OLIMEX/Neo6502/HARDWARE/Neo6502-rev-B1/3d/USB-A-SMT-6.3H_HOST_Female(87583-2010RLF).STEP

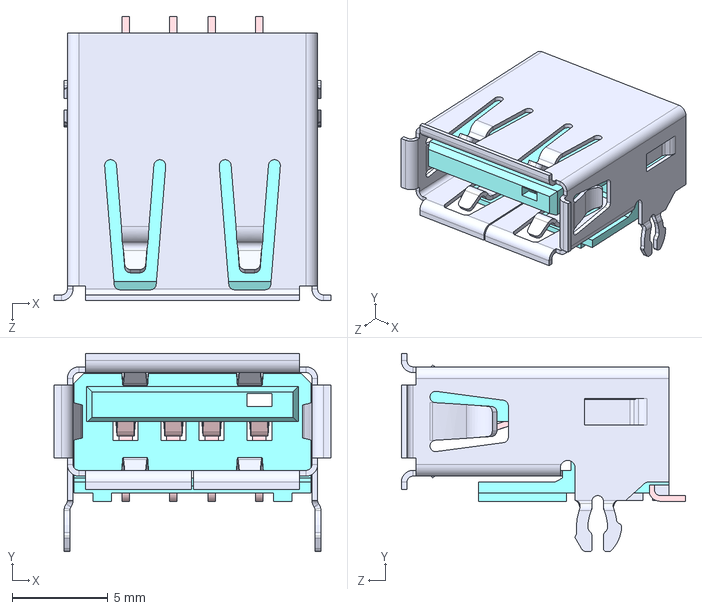
[picture p46: CAD file, 2023-08-04]
HARDWARE/Neo6502-rev-B1/3d/USB-A-SMT-6.3H_HOST_Female(87583-2010RLF).STEP
14.5 x 10.4 x 14.9 mm
