OLIMEX/Neo6502/HARDWARE/Neo6502-rev-B1/3d/USB-A-SMT-6.3H_HOST_Female(USB1046-GF-0190-L-B-A).STEP

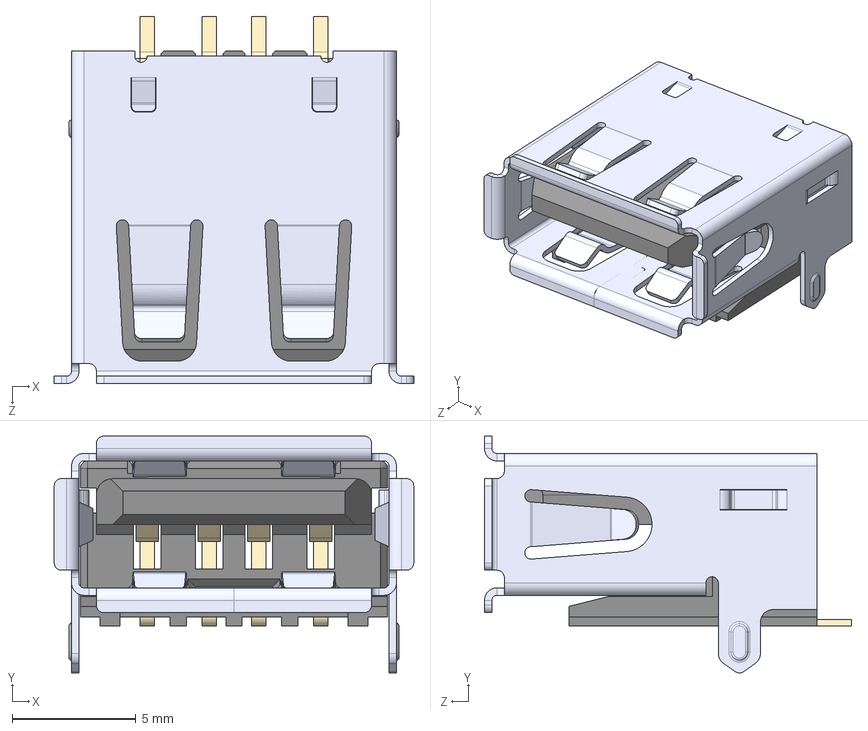
[picture p47: CAD file, 2023-08-04]
HARDWARE/Neo6502-rev-B1/3d/USB-A-SMT-6.3H_HOST_Female(USB1046-GF-0190-L-B-A).STEP
14.5 x 9.55 x 14.8 mm
