OLIMEX/Neo6502/HARDWARE/Neo6502-rev-B1/3d/SOT-23-5.step

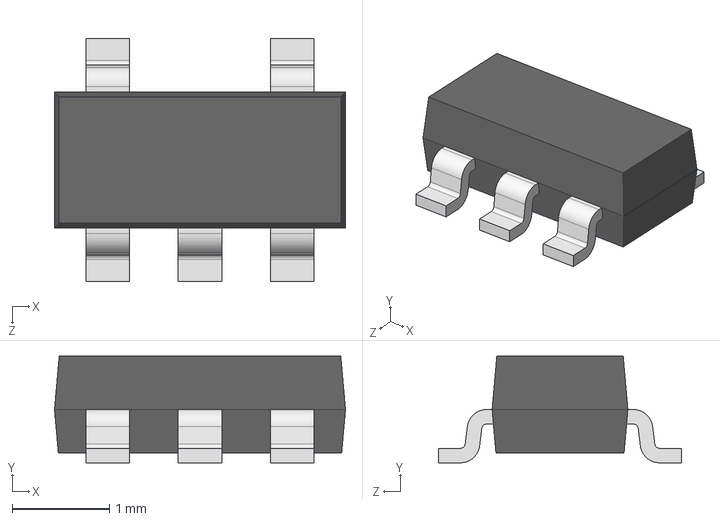
[picture p48: CAD file, 2023-08-04]
HARDWARE/Neo6502-rev-B1/3d/SOT-23-5.step
3.00 x 1.10 x 2.50 mm
