OLIMEX/Neo6502/HARDWARE/Neo6502-rev-B1/3d/HDMI_19POS_SMD_Wurth_Electronic-685119134923.stp

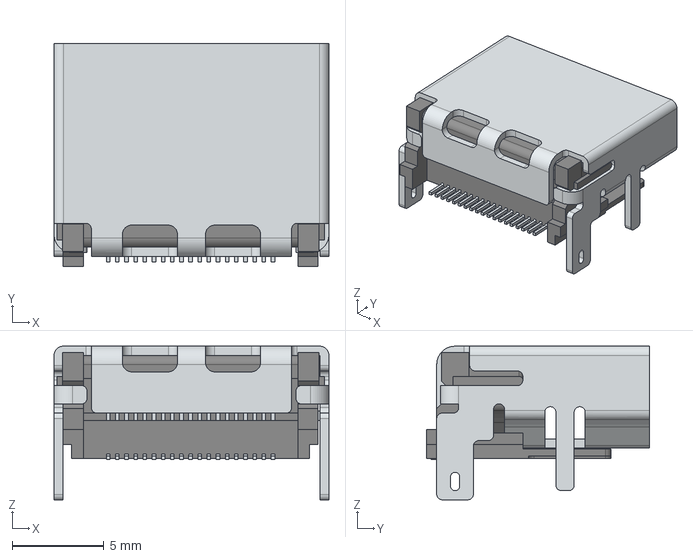
[picture p49: CAD file, 2023-08-04]
HARDWARE/Neo6502-rev-B1/3d/HDMI_19POS_SMD_Wurth_Electronic-685119134923.stp
15.0 x 12.2 x 8.38 mm
