OLIMEX/Neo6502/HARDWARE/Neo6502-rev-B1/3d/L-CD32_shielded.step

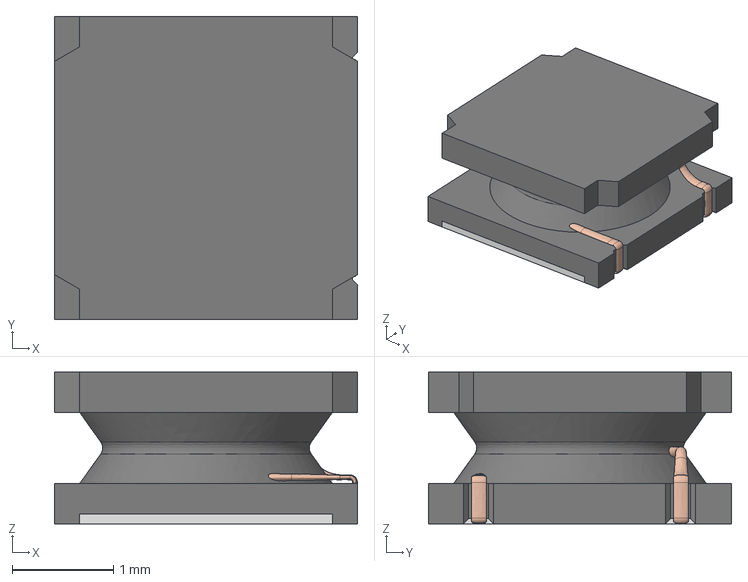
[picture p50: CAD file, 2023-08-04]
HARDWARE/Neo6502-rev-B1/3d/L-CD32_shielded.step
3.00 x 3.00 x 1.50 mm
