OLIMEX/Neo6502/HARDWARE/Neo6502-rev-B1/3d/SOT-23.step

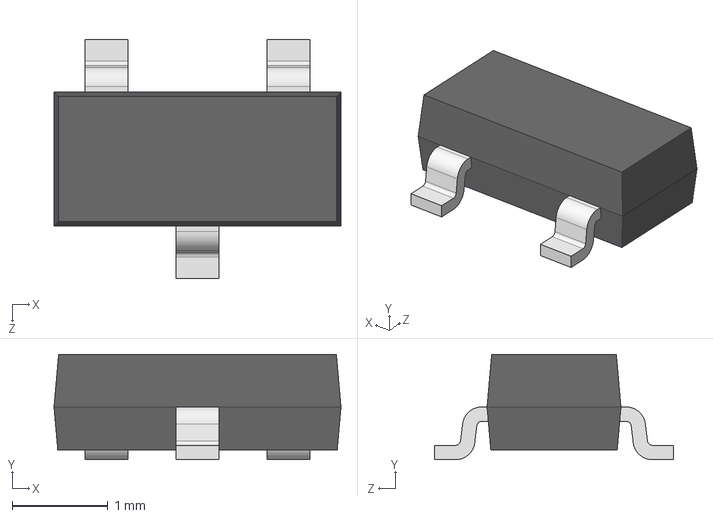
[picture p51: CAD file, 2023-08-04]
HARDWARE/Neo6502-rev-B1/3d/SOT-23.step
3.00 x 1.10 x 2.50 mm
