OLIMEX/Neo6502/SOFTWARE/Memory Emulator/NEO6502 v0.01/msbasic.cpp

// 
// Author: Rien Matthijsse
// 

#include "msbasic.h"

uint8_t msbasic_bin[] = {
	0x3f, 0xa6, 0x60, 0xa5, 0x43, 0xaa, 0x0c, 0xa7, 0x26, 0xa9, 0x04, 0xad, 0x52, 0xa9, 0xb9, 0xa7, 0xb9, 0xa6, 0x91, 0xa6, 0x3c, 0xa7, 0x23, 0xa6,
	0x9c, 0xa6, 0xe6, 0xa6, 0x4f, 0xa7, 0x3d, 0xa6, 0x5f, 0xa7, 0x80, 0xa6, 0x37, 0xb4, 0x68, 0xfd, 0xf6, 0xff, 0xe1, 0xaf, 0x2e, 0xb4, 0x2f, 0xa8,
	0x66, 0xa6, 0xbd, 0xa4, 0x80, 0xa4, 0x65, 0xa4, 0xe1, 0xb7, 0x6b, 0xb8, 0xfe, 0xb7, 0x0a, 0x00, 0xb1, 0xaf, 0xd2, 0xaf, 0xb5, 0xba, 0xc9, 0xbb,
	0xc3, 0xb5, 0x24, 0xbb, 0x05, 0xbc, 0x0c, 0xbc, 0x55, 0xbc, 0xa2, 0xbc, 0x24, 0xb4, 0x92, 0xb3, 0x90, 0xb0, 0xc3, 0xb3, 0xa1, 0xb3, 0x02, 0xb3,
	0x16, 0xb3, 0x42, 0xb3, 0x4d, 0xb3, 0x79, 0x74, 0xb4, 0x79, 0x5d, 0xb4, 0x7b, 0x03, 0xb6, 0x7b, 0xd5, 0xb6, 0x7f, 0xbe, 0xba, 0x50, 0x6c, 0xac,
	0x46, 0x69, 0xac, 0x7d, 0xf7, 0xba, 0x5a, 0xdb, 0xab, 0x64, 0x99, 0xac, 0x45, 0x4e, 0xc4, 0x46, 0x4f, 0xd2, 0x4e, 0x45, 0x58, 0xd4, 0x44, 0x41,
	0x54, 0xc1, 0x49, 0x4e, 0x50, 0x55, 0xd4, 0x44, 0x49, 0xcd, 0x52, 0x45, 0x41, 0xc4, 0x4c, 0x45, 0xd4, 0x47, 0x4f, 0x54, 0xcf, 0x52, 0x55, 0xce,
	0x49, 0xc6, 0x52, 0x45, 0x53, 0x54, 0x4f, 0x52, 0xc5, 0x47, 0x4f, 0x53, 0x55, 0xc2, 0x52, 0x45, 0x54, 0x55, 0x52, 0xce, 0x52, 0x45, 0xcd, 0x53,
	0x54, 0x4f, 0xd0, 0x4f, 0xce, 0x4e, 0x55, 0x4c, 0xcc, 0x57, 0x41, 0x49, 0xd4, 0x4c, 0x4f, 0x41, 0xc4, 0x53, 0x41, 0x56, 0xc5, 0x44, 0x45, 0xc6,
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
	0xea, 0xea, 0xea, 0xea, 0xea, 0xea, 0xea, 0xea, 0x29, 0x7f, 0xc9, 0x0f, 0xd0, 0x08, 0x48, 0xa5, 0x64, 0x49, 0xff, 0x85, 0x64, 0x68, 0x60, 0xa6,
	0xc3, 0xa0, 0x04, 0x84, 0x60, 0xbd, 0x00, 0x00, 0xc9, 0x20, 0xf0, 0x3b, 0x85, 0x5c, 0xc9, 0x22, 0xf0, 0x5a, 0x24, 0x60, 0x70, 0x31, 0xc9, 0x3f,
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
};
