OLIMEX/Neo6502/SOFTWARE/Memory Emulator/NEO6502 v0.01/ewoz.cpp

// 
// Author: Rien Matthijsse
// 

#include "ewoz.h"

uint8_t ewoz_bin[] = {
	0x20, 0xfc, 0x60, 0xfd, 0x46, 0xfd, 0x00, 0x00, 0x00, 0x00, 0x00, 0x00, 0x00, 0x00, 0x00, 0x00, 0x00, 0x00, 0x00, 0x00, 0x00, 0x00, 0x00, 0x00,
	0x00, 0x00, 0x00, 0x00, 0x00, 0x00, 0x00, 0x00, 0xd8, 0x58, 0xa2, 0xff, 0x9a, 0xa0, 0x7f, 0x8c, 0x12, 0xd0, 0xa9, 0xa7, 0x8d, 0x11, 0xd0, 0x8d,
	0x13, 0xd0, 0xa9, 0x0d, 0x20, 0x46, 0xfd, 0xa9, 0x50, 0x85, 0x2c, 0xa9, 0xfe, 0x85, 0x2d, 0x20, 0x53, 0xfd, 0xa9, 0x0d, 0x20, 0x46, 0xfd, 0xa9,
	0x9b, 0xc9, 0x88, 0xf0, 0x13, 0xc9, 0x9b, 0xf0, 0x03, 0xc8, 0x10, 0x19, 0xa9, 0xdc, 0x20, 0x46, 0xfd, 0xa9, 0x8d, 0x20, 0x46, 0xfd, 0xa0, 0x01,
	0x88, 0x30, 0xf6, 0xa9, 0xa0, 0x20, 0x46, 0xfd, 0xa9, 0x88, 0x20, 0x46, 0xfd, 0xad, 0x11, 0xd0, 0x10, 0xfb, 0xad, 0x10, 0xd0, 0x99, 0x00, 0x02,
	0x20, 0x46, 0xfd, 0xc9, 0x8d, 0xd0, 0xca, 0xa0, 0xff, 0xa9, 0x00, 0xaa, 0x0a, 0x85, 0x2b, 0xc8, 0xb9, 0x00, 0x02, 0xc9, 0x8d, 0xf0, 0xca, 0xc9,
	0xae, 0x90, 0xf4, 0xf0, 0xf0, 0xc9, 0xba, 0xf0, 0xeb, 0xc9, 0xd2, 0xf0, 0x31, 0xc9, 0xcc, 0xf0, 0x36, 0x86, 0x28, 0x86, 0x29, 0x84, 0x2a, 0xb9,
	0x00, 0x02, 0x49, 0xb0, 0xc9, 0x0a, 0x90, 0x06, 0x69, 0x88, 0xc9, 0xfa, 0x90, 0x11, 0x0a, 0x0a, 0x0a, 0x0a, 0xa2, 0x04, 0x0a, 0x26, 0x28, 0x26,
	0x29, 0xca, 0xd0, 0xf8, 0xc8, 0xd0, 0xe0, 0xc4, 0x2a, 0xd0, 0x12, 0x4c, 0x54, 0xfc, 0x20, 0xd4, 0xfc, 0x4c, 0x47, 0xfc, 0x6c, 0x24, 0x00, 0x20,
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
	0x20, 0x48, 0x65, 0x78, 0x20, 0x49, 0x6d, 0x70, 0x6f, 0x72, 0x74, 0x65, 0x64, 0x20, 0x77, 0x69, 0x74, 0x68, 0x20, 0x63, 0x68, 0x65, 0x63, 0x6b,
	0x73, 0x75, 0x6d, 0x20, 0x65, 0x72, 0x72, 0x6f, 0x72, 0x2e, 0x00 };
