OLIMEX/Neo6502/SOFTWARE/Memory Emulator/NEO6502 v0.01/mon_ext.cpp

// 
// Author: Rien Matthijsse
// 

#include "mon_ext.h"

uint8_t mon_ext_bin[] = {
	0xa9, 0x14, 0x48, 0x20, 0x73, 0xf1, 0x20, 0x37, 0xf2, 0x85, 0x0a, 0x84, 0x0b, 0x68, 0x38, 0xe9, 0x01, 0xd0, 0xef, 0x20, 0xfe, 0xf1, 0x8a, 0xd0,
	0x03, 0x4c, 0x54, 0xfc, 0xa0, 0x00, 0x20, 0x46, 0xf2, 0x48, 0x8a, 0xf0, 0x07, 0xb5, 0x0c, 0x95, 0x0a, 0xca, 0x10, 0xf9, 0x68, 0xc9, 0x05, 0xf0,
	0xcf, 0xc9, 0x99, 0xf0, 0x04, 0xc9, 0x93, 0xd0, 0x76, 0xa9, 0x03, 0x85, 0x0d, 0x20, 0x26, 0xf2, 0x0a, 0xe9, 0xbe, 0xc9, 0xc2, 0x90, 0x68, 0x0a,
	0x0a, 0xa2, 0x04, 0x0a, 0x26, 0x12, 0x26, 0x13, 0xca, 0x10, 0xf8, 0xc6, 0x0d, 0xf0, 0xf4, 0x10, 0xe4, 0xa2, 0x05, 0x20, 0x26, 0xf2, 0x84, 0x1a,
	0xdd, 0xc6, 0xf2, 0xd0, 0x13, 0x20, 0x26, 0xf2, 0xdd, 0xcc, 0xf2, 0xf0, 0x0d, 0xbd, 0xcc, 0xf2, 0xf0, 0x07, 0xc9, 0xa4, 0xf0, 0x03, 0xa4, 0x1a,
	0x18, 0x88, 0x26, 0x07, 0xe0, 0x03, 0xd0, 0x0d, 0x20, 0x46, 0xf2, 0xa5, 0x0f, 0xf0, 0x01, 0xe8, 0x86, 0x18, 0xa2, 0x03, 0x88, 0x86, 0x0d, 0xca,
	0x10, 0xc9, 0xa5, 0x07, 0x0a, 0x0a, 0x05, 0x18, 0xc9, 0x20, 0xb0, 0x06, 0xa6, 0x18, 0xf0, 0x02, 0x09, 0x80, 0x85, 0x07, 0x84, 0x1a, 0xb9, 0x00,
	0x02, 0xc9, 0xbb, 0xf0, 0x04, 0xc9, 0x8d, 0xd0, 0x2c, 0xa5, 0x0d, 0x20, 0x2d, 0xf1, 0xaa, 0xbd, 0x12, 0xf3, 0xc5, 0x12, 0xd0, 0x13, 0xbd, 0xd2,
	0xf2, 0xc5, 0x13, 0xd0, 0x0c, 0xa5, 0x07, 0xa4, 0x05, 0xc0, 0x9d, 0xf0, 0x20, 0xc5, 0x05, 0xf0, 0x37, 0xc6, 0x0d, 0xd0, 0xdc, 0xe6, 0x07, 0xc6,
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
	0xa4, 0x8a, 0x00, 0xaa, 0xa2, 0xa2, 0x74, 0x74, 0x74, 0x72, 0x44, 0x68, 0xb2, 0x32, 0xb2, 0x00, 0x22, 0x00, 0x1a, 0x1a, 0x26, 0x26, 0x72, 0x72,
	0x88, 0xc8, 0xc4, 0xca, 0x26, 0x48, 0x44, 0x44, 0xa2, 0xc8};
