OLIMEX/Neo6502/SOFTWARE/Memory Emulator/NEO6502 v0.01/m6821.cpp

// 
// Author: Rien Matthijsse
// 

#include "m6821.h"

byte regKBD;
byte regKBDDIR;    // Dir register when KBDCR.bit2 == 0
byte regKBDCR;
byte regDSP;
byte regDSPDIR;    // Dir register when DSPCR.bit2 == 0
byte regDSPCR;


/// <summary>
/// 
/// </summary>
void init6821()
{
  regKBD = 0x00;
  regKBDDIR = 0x00;
  regKBDCR = 0x00;
  regDSP = 0x00;
  regDSPDIR = 0x00;
  regDSPCR = 0x00;
}
