OLIMEX/Neo6502/SOFTWARE/Memory Emulator/NEO6502 v0.01/mos65C02.h

// 
// Author: Rien Matthijsse
// 

#ifndef _MOS65C02_h
#define _MOS65C02_h

#include "arduino.h"
#include "pins.h"
#include "memory.h"

//#define TEST_MODE

#define CPU_DEBUG   1


#define RESET_LOW   false
#define RESET_HIGH  true

#define ENABLE_LOW  false
#define ENABLE_HIGH true

#define CLOCK_LOW   false
#define CLOCK_HIGH  true

#define RW_READ     true
#define RW_WRITE    false

void init6502();
void reset6502();
void tick6502(uint32_t);
#ifdef TEST_MODE
void test6502();
#endif

#endif
